AguaClara/Fluoride_Gravity-DEPRECATED/Fall 2018/Gravity_Apparatus_Frame_dimensions.pdf

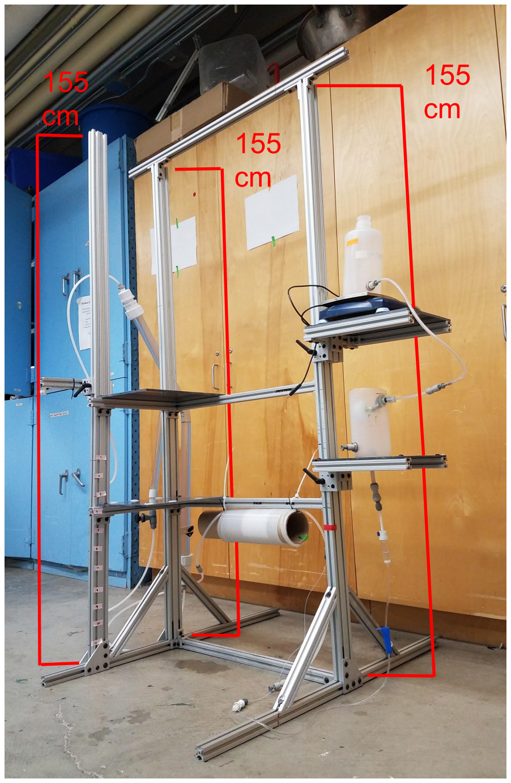
[picture p45: page 1]

155
cm
155
cm

155
cm
