AguaClara/Fluoride_Gravity-DEPRECATED/Fall 2018/Drip_chamber.jpg

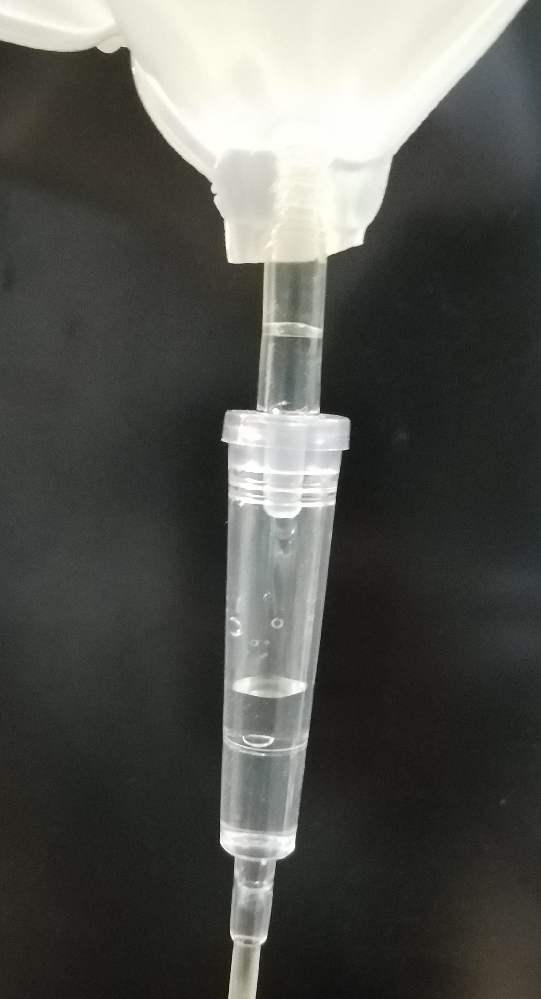
Fall 2018/Drip_chamber.jpg
