AguaClara/Fluoride_Gravity-DEPRECATED/Fall 2018/Fall2018data/scale flow rate 15cm nov27.PNG

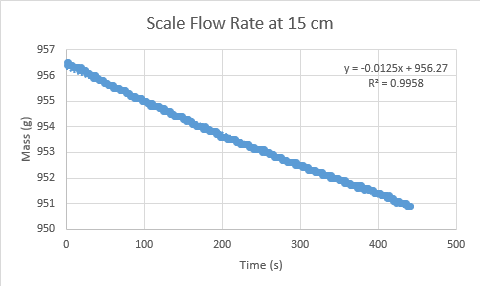
Fall 2018/Fall2018data/scale flow rate 15cm nov27.PNG
