AguaClara/Fluoride_Gravity-DEPRECATED/Fall 2018/Fall2018data/scale flow rate 25cm nov27.PNG

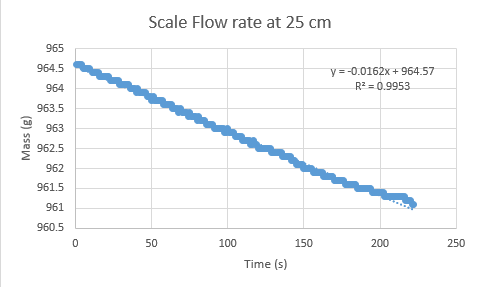
Fall 2018/Fall2018data/scale flow rate 25cm nov27.PNG
