AguaClara/Fluoride_Gravity-DEPRECATED/Fall 2018/Fall2018data/Scale_flow_rate_20cm.PNG

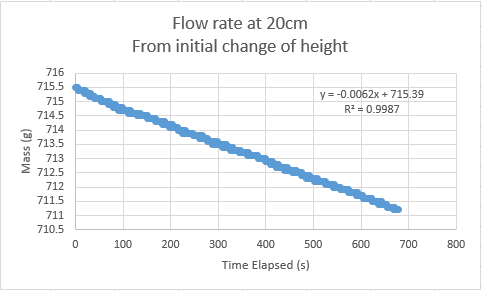
Fall 2018/Fall2018data/Scale_flow_rate_20cm.PNG
