AguaClara/Fluoride_Gravity-DEPRECATED/Fall 2018/Fall2018data/scale_flow_rate_20cm_adjusted.PNG

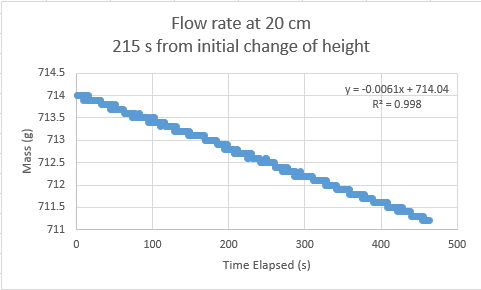
Fall 2018/Fall2018data/scale_flow_rate_20cm_adjusted.PNG
