AguaClara/Fluoride_Gravity-DEPRECATED/Fall 2018/Fall2018data/Scale_flow_rate_30cm_height_raw.PNG

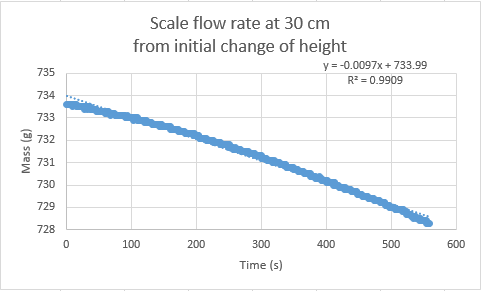
Fall 2018/Fall2018data/Scale_flow_rate_30cm_height_raw.PNG
