AguaClara/Fluoride_Gravity-DEPRECATED/Fall 2018/Gravity_reactor_labeled_edit.jpg

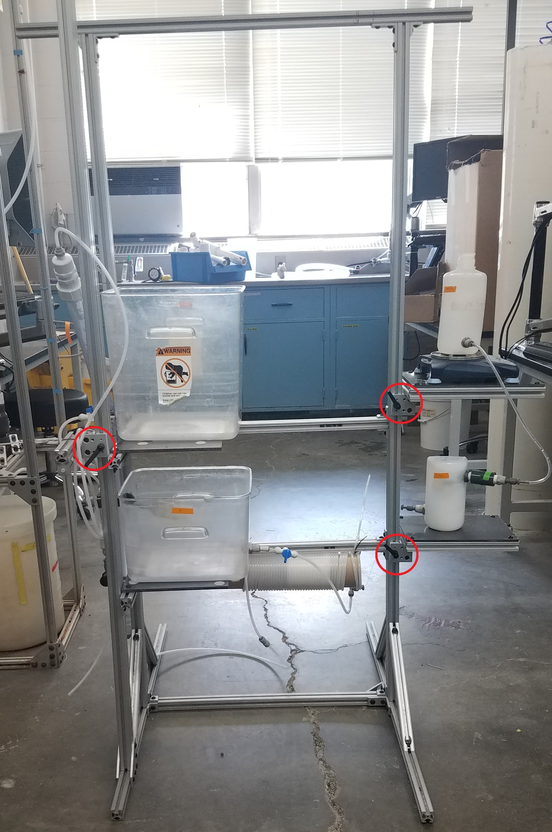
Fall 2018/Gravity_reactor_labeled_edit.jpg
