AguaClara/Fluoride_Gravity-DEPRECATED/Fall 2018/IVbag (2).jpg

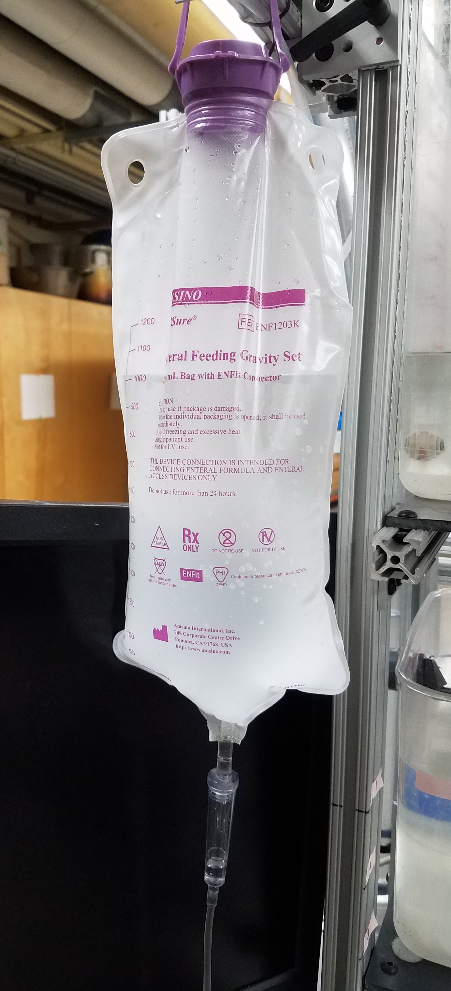
Fall 2018/IVbag (2).jpg
