AguaClara/Fluoride_Gravity-DEPRECATED/Fall 2018/IVbag.jpg

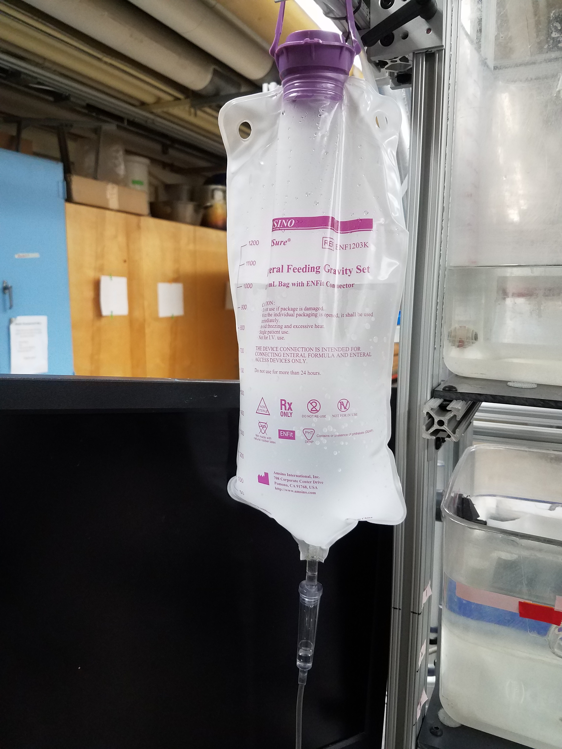
Fall 2018/IVbag.jpg
