AguaClara/Fluoride_Gravity-DEPRECATED/Spring 2019/Fit with Langmuir Isotherm 2018.PNG

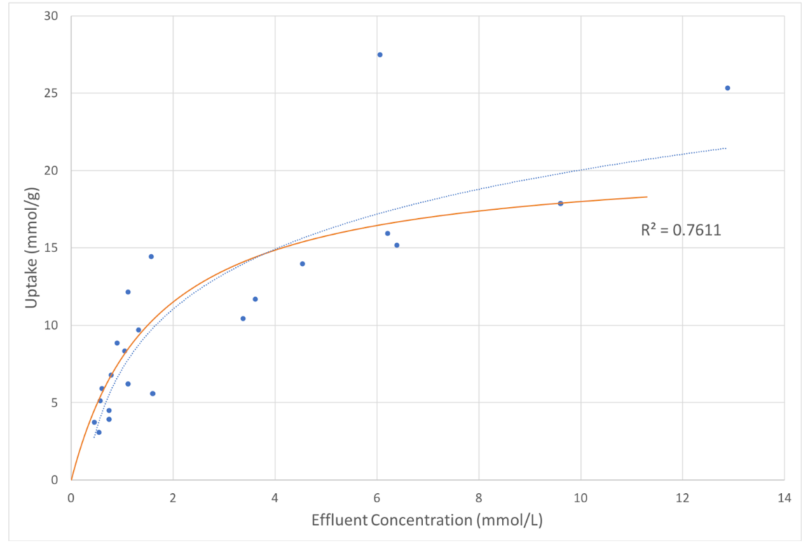
Spring 2019/Fit with Langmuir Isotherm 2018.PNG
