AguaClara/Fluoride_Gravity-DEPRECATED/Spring 2019/Fit with Langmuir Isotherm.PNG

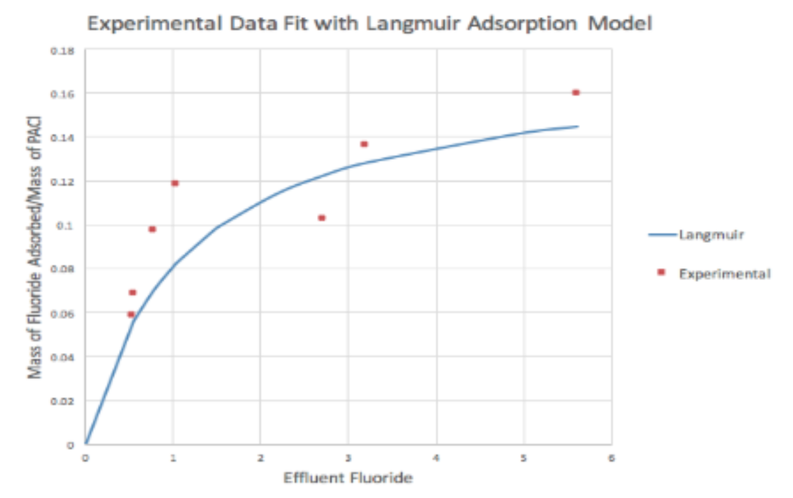
Spring 2019/Fit with Langmuir Isotherm.PNG
