AguaClara/Fluoride_Gravity-DEPRECATED/Spring 2019/IMG_20190209_092106.jpg

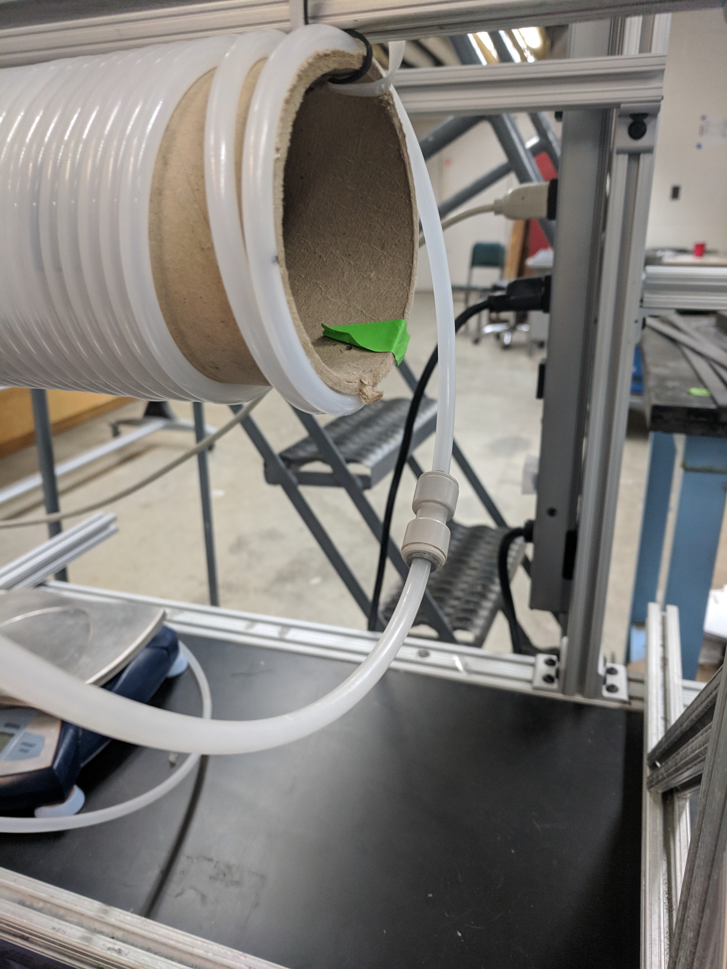
Spring 2019/IMG_20190209_092106.jpg
