AguaClara/Fluoride_Gravity-DEPRECATED/Spring 2019/IMG_20190209_092113.jpg

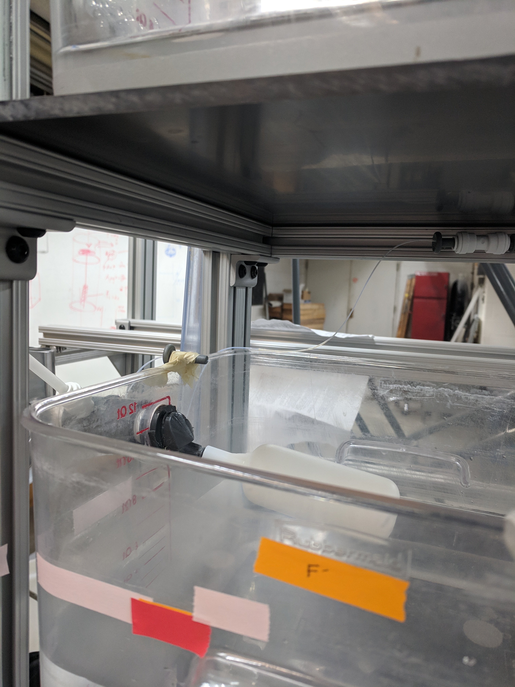
Spring 2019/IMG_20190209_092113.jpg
